Mellerayba/StudyWithKey/Physical-Prototypes/Bluetooth-Connection.jpeg

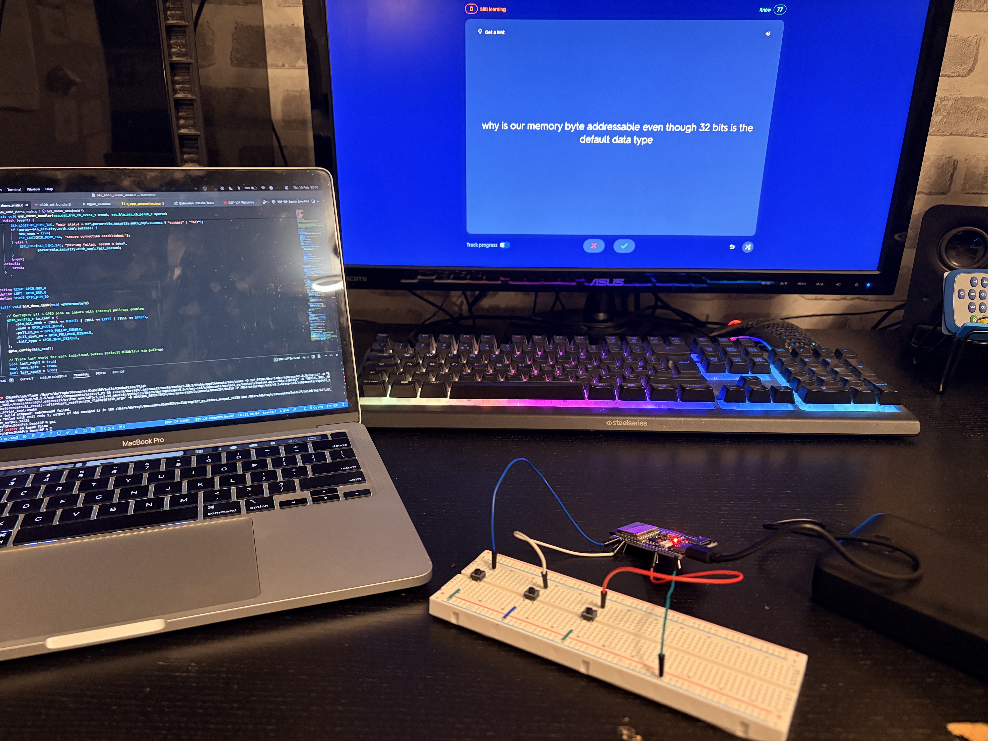
Physical-Prototypes/Bluetooth-Connection.jpeg
