Mellerayba/StudyWithKey/Physical-Prototypes/PhysicalDocs/PhysicalPCB/2.bmp

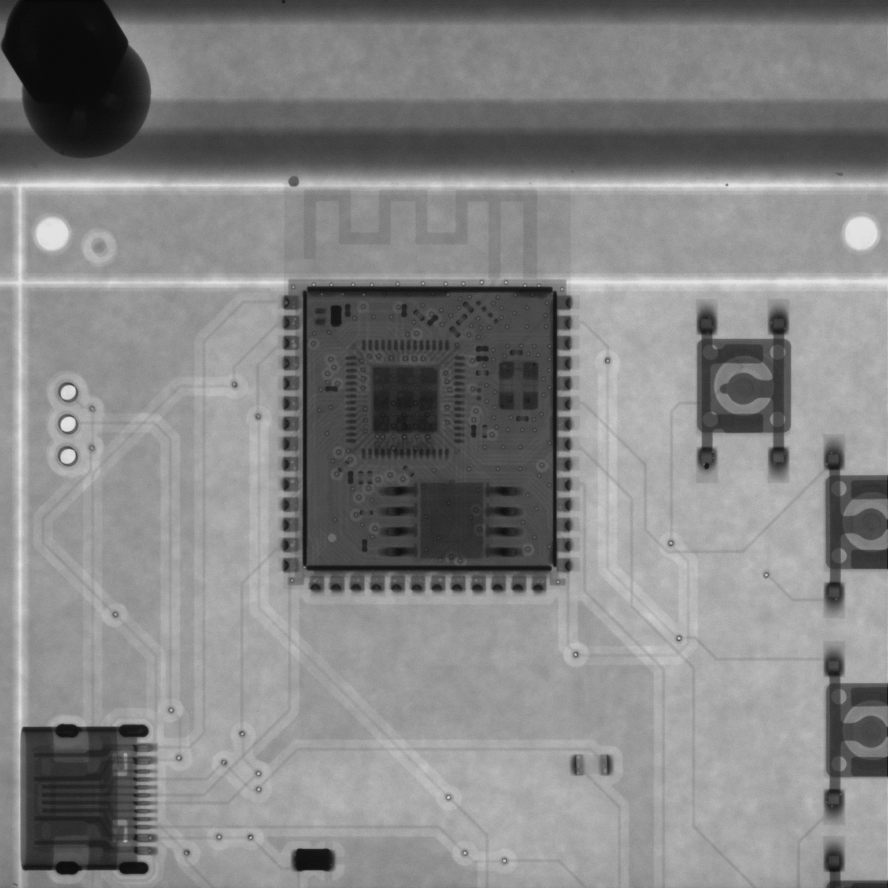
Physical-Prototypes/PhysicalDocs/PhysicalPCB/2.bmp
