Mellerayba/StudyWithKey/Physical-Prototypes/PhysicalDocs/PhysicalPCB/3.bmp

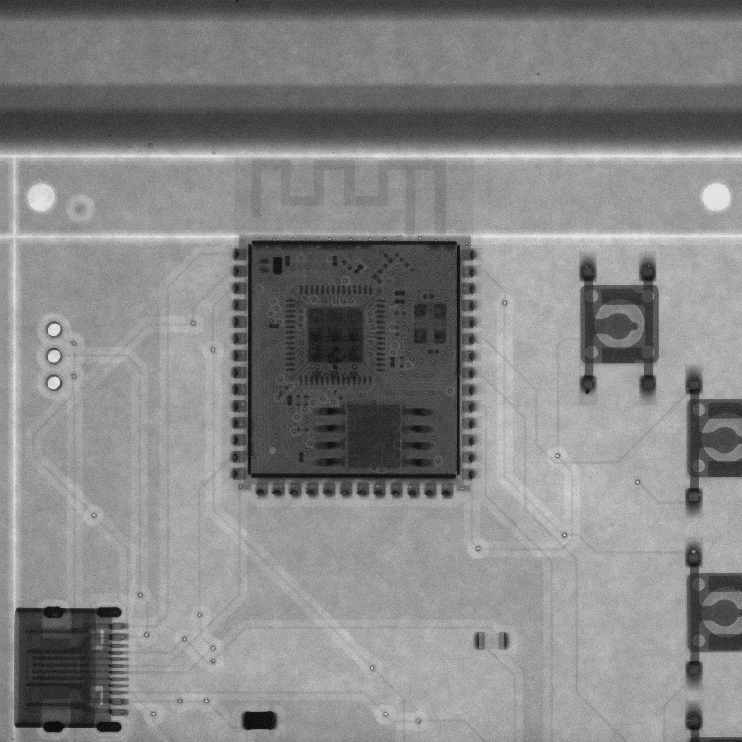
Physical-Prototypes/PhysicalDocs/PhysicalPCB/3.bmp
