Mellerayba/StudyWithKey/Physical-Prototypes/PhysicalDocs/PhysicalPCB/4.bmp

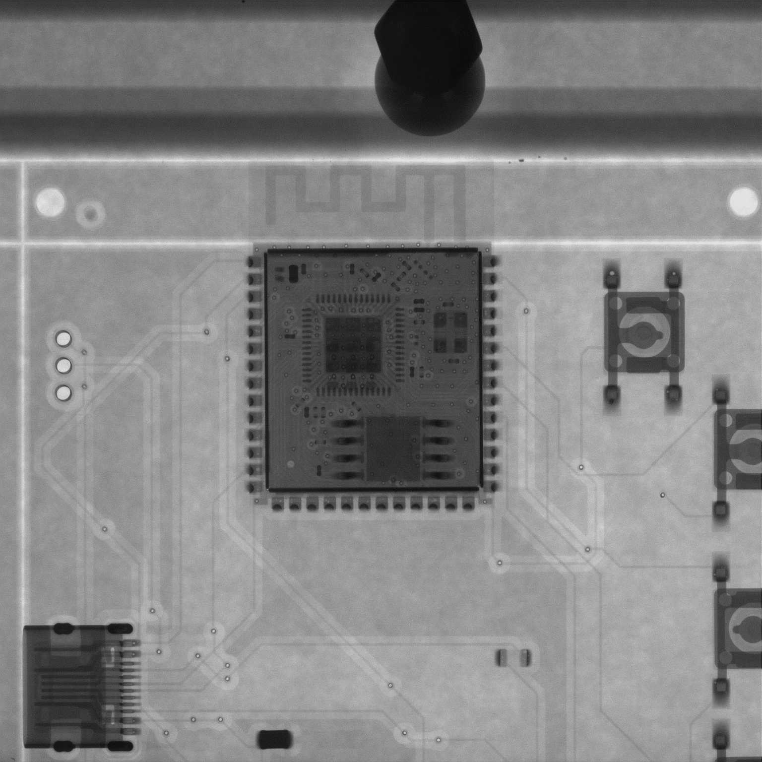
Physical-Prototypes/PhysicalDocs/PhysicalPCB/4.bmp
